bricktrooper/Dexterity/software/serial.c

#include <stdio.h>
#include <string.h>
#include <errno.h>
#include <unistd.h>
#include <fcntl.h>
#include <termios.h>
#include <stdbool.h>

#include "dexterity.h"
#include "serial.h"
#include "log.h"

#define SERIAL_PORT       "/dev/cu.usbserial-AQ00PEW7"    // Use 'cu' instead of 'tty' to prevent DCD (data-carrier-detect)
#define SERIAL_CLOSED     -1                              // Invalid file descriptor for closed serial port
#define RX_READ_TIMEOUT    10                             // timeout in deciseconds (10^-1 s)
#define TX_WRITE_DELAY     100                            // delay in microseconds between 1B writes to TX (used to avoid RX buffer overrun on PIC)
#define BAUD_RATE          B115200                        // transfer rate of the serial port

extern int errno;

static int serial_port = SERIAL_CLOSED;
static struct termios settings;

int serial_open(void)
{
	int result = ERROR;

	if (serial_is_open())
	{
		log(LOG_WARNING, "The serial port is already open\n");
		return WARNING;
	}

	// OPEN SERIAL PORT //

	serial_port = open(SERIAL_PORT, O_RDWR);
	tcflush(serial_port, TCIOFLUSH);   // Discard any old data from RX and TX buffer

	if (serial_port < 0)
	{
		log(LOG_ERROR, "Failed to open serial port '%s': %s (%d)\n", SERIAL_PORT, strerror(errno), errno);
		return ERROR;
	}

	log(LOG_DEBUG, "Opened serial port '%s'\n", SERIAL_PORT);

	// GET SERIAL PORT ATTRIBUTES //

	if (tcgetattr(serial_port, &settings) != 0)
	{
		log(LOG_ERROR, "Failed to get serial port attributes: %s (%d)\n", strerror(errno), errno);
		goto EXIT;
	}

	// APPLY SETTINGS //

	// The serial settings are specified by applying the following masks to the appropriate flags.
	// Use these masks to either set or clear settings.
	// Code adapted from https://blog.mbedded.ninja/programming/operating-systems/linux/linux-serial-ports-using-c-cpp/#overview

	// LOCAL //
	settings.c_lflag &= ~ICANON;    // disable canonical mode (newline delimiter)
	settings.c_lflag &= ~ISIG;      // disable interpretation of INTR, QUIT and SUSP characters
	settings.c_lflag &= ~IEXTEN;    // disable input processing
	settings.c_lflag &= ~ECHO;      // disable echo
	settings.c_lflag &= ~ECHOE;     // disable erasure
	settings.c_lflag &= ~ECHOK;     // disable kill erasure
	settings.c_lflag &= ~ECHONL;    // disable newline echo
	settings.c_iflag &= ~IXON;      // disable output flow control
	settings.c_iflag &= ~IXOFF;     // disable input flow control
	settings.c_iflag &= ~IXANY;     // disable restart flow control

	// CONTROL //
	settings.c_cflag &= ~PARENB;    // disable parity
	settings.c_cflag &= ~CSTOPB;    // use one stop bit
	settings.c_cflag &= ~CSIZE;     // clear data size (bits per byte)
	settings.c_cflag &= ~CRTSCTS;   // Disable RTS/CTS
	settings.c_cflag |= CS8;        // set data size to 8 bits per byte
	settings.c_cflag |= CREAD;      // Enable reading
	settings.c_cflag |= CLOCAL;     // ignore control signals

	// OUTPUT //
	settings.c_oflag &= ~OPOST;     // Disable special interpretation of output bytes (e.g. newline)
	settings.c_oflag &= ~ONLCR;     // Disable conversion of newline to carriage return/line feed
	settings.c_oflag &= ~OXTABS;    // Disable conversion of tabs to spaces
	settings.c_oflag &= ~ONOEOT;    // Disable removal of C-d chars (0x004) in output

	// INPUT //
	// disable special handling of received bytes and get raw data instead
	settings.c_iflag &= ~IGNBRK;
	settings.c_iflag &= ~BRKINT;
	settings.c_iflag &= ~PARMRK;
	settings.c_iflag &= ~ISTRIP;
	settings.c_iflag &= ~INLCR;
	settings.c_iflag &= ~IGNCR;
	settings.c_iflag &= ~ICRNL;

	// SPECIAL CHARACTERS //
	settings.c_cc[VTIME] = RX_READ_TIMEOUT;   // Timeout in deciseconds (10^-1 s) before timeout
	settings.c_cc[VMIN] = 0;                  // blocking

	// BAUD RATE //

	if (cfsetispeed(&settings, BAUD_RATE) < 0)   // Set input baud rate to 115200
	{
		log(LOG_ERROR, "Failed to set input baud rate to %d: %s (%d)\n", BAUD_RATE, strerror(errno), errno);
		goto EXIT;
	}

	if (cfsetospeed(&settings, BAUD_RATE) < 0)   // Set output baud rate to 115200
	{
		log(LOG_ERROR, "Failed to set output baud rate to %d: %s (%d)\n", BAUD_RATE, strerror(errno), errno);
		goto EXIT;
	}

	log(LOG_DEBUG, "Set baud rate to %u\n", BAUD_RATE);

	// SAVE ATTRIBUTES //

	if (tcsetattr(serial_port, TCSANOW, &settings) != 0)
	{
		log(LOG_ERROR, "Failed to set serial port attributes: %s (%d)\n", strerror(errno), errno);
	}

	log(LOG_DEBUG, "Configured serial port attributes\n");
	result = SUCCESS;

EXIT:
	if (result == ERROR)
	{
		serial_close();
	}

	return result;
}

int serial_close(void)
{
	if (!serial_is_open())
	{
		log(LOG_WARNING, "The serial port is not open\n");
		return WARNING;
	}

	close(serial_port);
	serial_port = -1;
	log(LOG_DEBUG, "Closed serial port '%s'\n", SERIAL_PORT);

	return SUCCESS;
}

bool serial_is_open(void)
{
	return (serial_port != SERIAL_CLOSED);
}

int serial_purge(void)
{
	if (!serial_is_open())
	{
		log(LOG_ERROR, "The serial port is not open\n");
		return ERROR;
	}

	if (tcflush(serial_port, TCIFLUSH) == ERROR)
	{
		log(LOG_ERROR, "Failed to purge serial port RX buffer: %s (%d)\n", strerror(errno), errno);
		return ERROR;
	}

	return SUCCESS;
}

int serial_read(void * buffer, int size)
{
	if (buffer == NULL || size < 0)
	{
		log(LOG_ERROR, "Invalid arguments\n");
		return ERROR;
	}

	if (!serial_is_open())
	{
		log(LOG_ERROR, "The serial port is not open\n");
		return ERROR;
	}

	char * data = (char *)buffer;
	int received = 0;

	do
	{
		int result = read(serial_port, data + received, size - received);

		if (result == 0)   // done reading
		{
			break;
		}
		else if (result < 0)   // error
		{
			received = result;
			break;
		}

		received += result;
	}
	while (received < size);

	if (received != size)
	{
		if (errno == ETIMEDOUT)
		{
			// A timeout is not a fatal error (the user may want to try reading again)
			log(LOG_WARNING, "Failed to read from serial port: %s (%d)\n", strerror(errno), errno);
		}
		else
		{
			log(LOG_ERROR, "Failed to read from serial port: %s (%d)\n", strerror(errno), errno);
			return ERROR;
		}
	}

	log(LOG_DEBUG, "Read %dB from the serial port\n", received);
	return received;
}

int serial_write(void * buffer, int size)
{
	if (buffer == NULL || size < 0)
	{
		log(LOG_ERROR, "Invalid arguments\n");
		return ERROR;
	}

	if (!serial_is_open())
	{
		log(LOG_ERROR, "The serial port is not open\n");
		return ERROR;
	}

	if (serial_purge() == ERROR)
	{
		log(LOG_ERROR, "Failed to purge the serial port before writing new data\n");
		return ERROR;
	}

	char * data = (char *)buffer;
	int transmitted = 0;

	for (int i = 0; i < size; i++)
	{
		int result = write(serial_port, data + i, 1);
		tcdrain(serial_port);
		usleep(TX_WRITE_DELAY);

		if (result == 0)   // done writing
		{
			break;
		}
		else if (result < 0)   // error
		{
			transmitted = result;
			break;
		}
		else   // continue writing
		{
			transmitted += result;
		}
	}

	if (transmitted != size)
	{
		log(LOG_ERROR, "Failed to write to serial port: %s (%d)\n", strerror(errno), errno);
		return ERROR;
	}

	log(LOG_DEBUG, "Wrote %dB to the serial port\n", transmitted);
	return transmitted;
}

Message serial_read_message(void)
{
	char next = 0;
	char data [MAX_MESSAGE_SIZE + 1];
	int length = sizeof(data);

	memset(data, 0, length);

	for (int i = 0; i < length - 1; i++)
	{
		if (serial_read(&next, 1) != 1)  // read 1B at a time
		{
			log(LOG_ERROR, "Failed to read message character #%d\n", i + 1);
			return MESSAGE_UNKNOWN;
		}

		if (next == '\r')   // carriage return [Enter] indicates end of transmission
		{
			break;
		}

		data[i] = next;
	}

	for (Message message = 0; message < NUM_MESSAGES; message++)
	{
		char * string = message_string(message);

		if (strncmp(data, string, strlen(string)) == 0)
		{
			log(LOG_DEBUG, "Received message from device: '%s'\n", string);
			return message;
		}
	}

	log(LOG_WARNING, "Received unknown message from device: '%s'\n", data);
	return MESSAGE_UNKNOWN;
}

int serial_write_message(Message message)
{
	char * string = message_string(message);
	int length = strlen(string);
	char data [MAX_MESSAGE_SIZE];

	memcpy(data, string, length);   // load message string
	memcpy(data + length, "\r", 1); // carriage return [Enter] indicates end of transmission
	length += 1;                    // length of message including the terminator

	if (serial_write(data, length) != length)
	{
		log(LOG_ERROR, "Failed to write message to serial port: '%s'\n", string);
		return ERROR;
	}

	log(LOG_DEBUG, "Sent message to device: '%s'\n", string);
	return SUCCESS;
}
