bricktrooper/Dexterity/software/colours.h

/* This header contains string substitutions
 * for ANSI terminal colours. */

#ifndef COLOURS_H
#define COLOURS_H

#define BLACK     "\033[0;30m"
#define RED       "\033[0;31m"
#define GREEN     "\033[0;32m"
#define YELLOW    "\033[0;33m"
#define BLUE      "\033[0;34m"
#define MAGENTA   "\033[0;35m"
#define CYAN      "\033[0;36m"
#define WHITE     "\033[0;37m"
#define RESET     "\033[0m"

#endif /* COLOURS_H */
