bricktrooper/Dexterity/firmware/adc.h

#ifndef ADC_H
#define ADC_H

#define ADC_MIN   0
#define ADC_MAX   1023

enum VREF
{
	VREF_INTERNAL = 0,
	VREF_EXTERNAL = 1
};

typedef enum VREF VREF;

void adc_init(void);
void adc_run(void);
S16 adc_read(int channel);
int adc_channel(int channel);
void adc_vref(VREF vref);

#endif /* ADC_H */
