bricktrooper/Dexterity/firmware/button.c

#include <xc.h>
#include <pic16f690.h>

#include "dexterity.h"
#include "pins.h"

#include "button.h"

void button_init(void)
{
	BUTTON_TRIS = 1;   // set button as input
}

int button_pressed(void)
{
	return BUTTON;
}

int button_released(void)
{
	return !BUTTON;
}

void button_wait_for_press(void)
{
	while (button_released());
}

void button_wait_for_release(void)
{
	while (button_pressed());
}

void button_wait_for_click(void)
{
	button_wait_for_press();
	button_wait_for_release();
}
